EstebanSannin/esp32-m2-companion/hardware/tools/view_defs.py

"""Callout definitions shared by gen_views (figures) and gen_datasheet
(legend tables) so they cannot drift apart."""

TOP_CALLOUTS = [
    ("U2", "ESP32-S3-WROOM-1-N8R2 module"),
    ("ANT", "Module PCB antenna + RF keep-out zone"),
    ("J4", "J4 - UART / SPI / GPIO (JST SH-8, top entry)"),
    ("J3", "J3 - Qwiic / STEMMA-QT I2C (JST SH-4, top entry)"),
    ("J1", "M.2 Key-B card edge (75-pos, USB 2.0 + sidebands)"),
    ("SCR", "Mounting notch (M.2 screw, GND pad)"),
]
BOT_CALLOUTS = [
    ("U1", "USBLC6-2 USB ESD protection"),
    ("FB1", "3.3 V entry filter + bulk capacitors"),
    ("D1", "Recovery diodes (EN / IO0 sideband isolation)"),
    ("TP1", "Test points: EN, IO0, TXD0, RXD0, 3V3, GND"),
    ("R7", "USB series resistors (0R)"),
    ("D3", "Power LED (green, side-view, emits from left edge)"),
    ("D4", "Status LED (red, IO48, side-view, emits from left edge)"),
    ("C6", "Module 3V3 decoupling"),
    ("R5", "DNP provisions (I2C pull-ups, USB shunt C)"),
]
